mr-foxi/RemiRAT/Schem.png

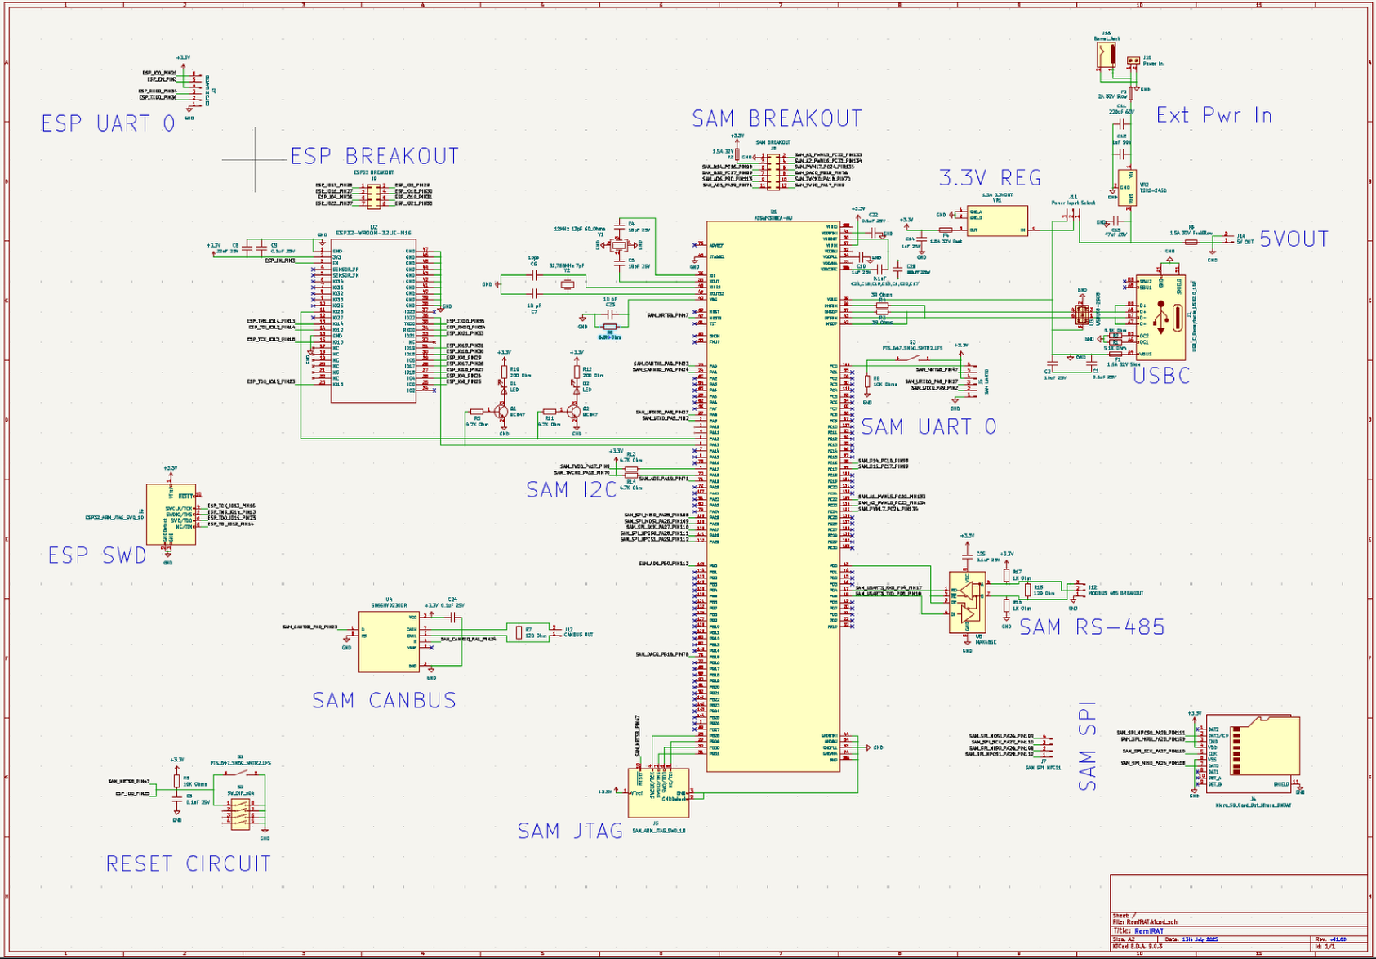
Schem.png
