mr-foxi/RemiRAT/Schem_02.png

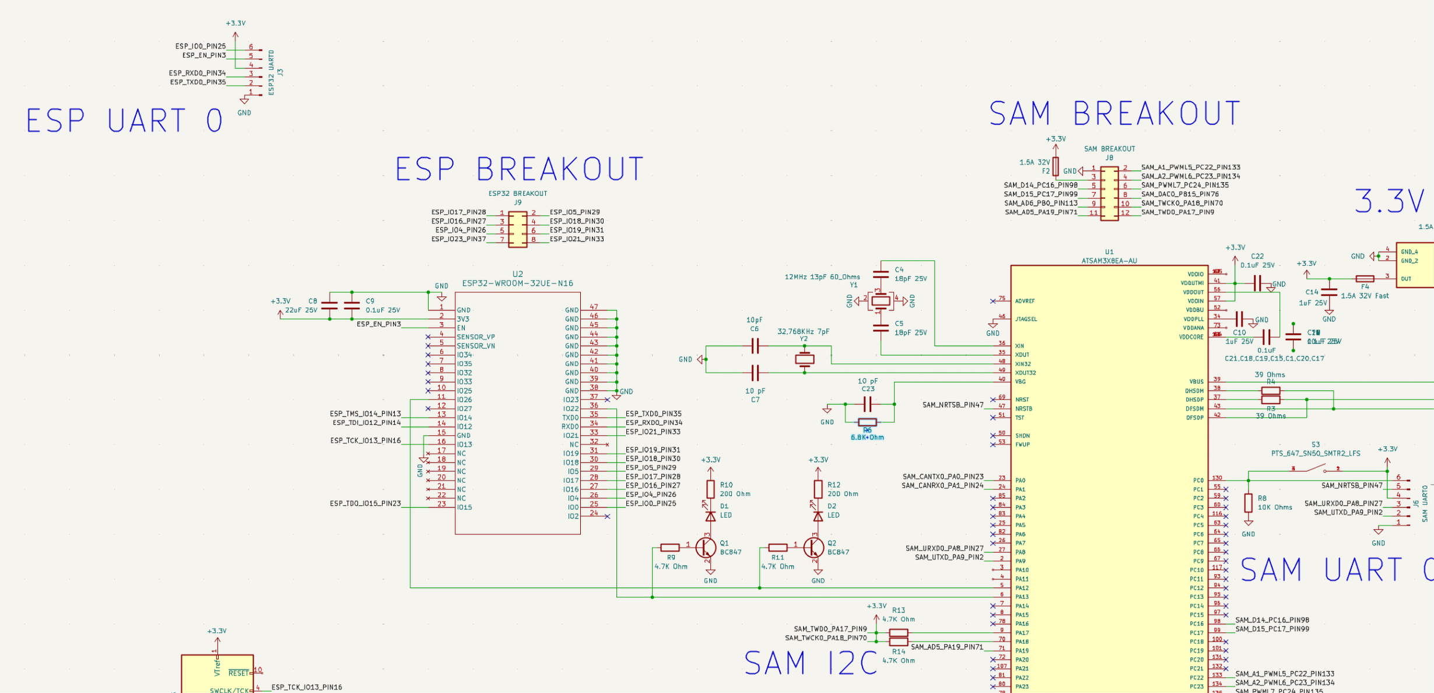
Schem_02.png
