mr-foxi/RemiRAT/SilkScreen_TOP.png

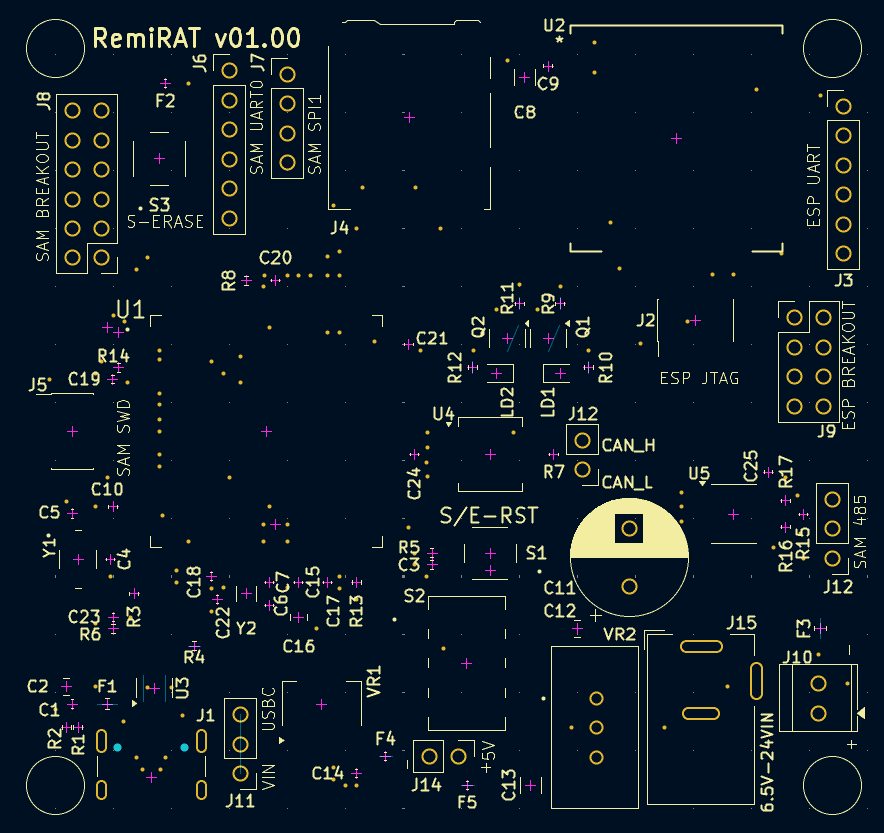
SilkScreen_TOP.png
